cero97-ctrl/LCR-METER/LC-Meter/materiel/DO-35 Diode Horizontal.stp

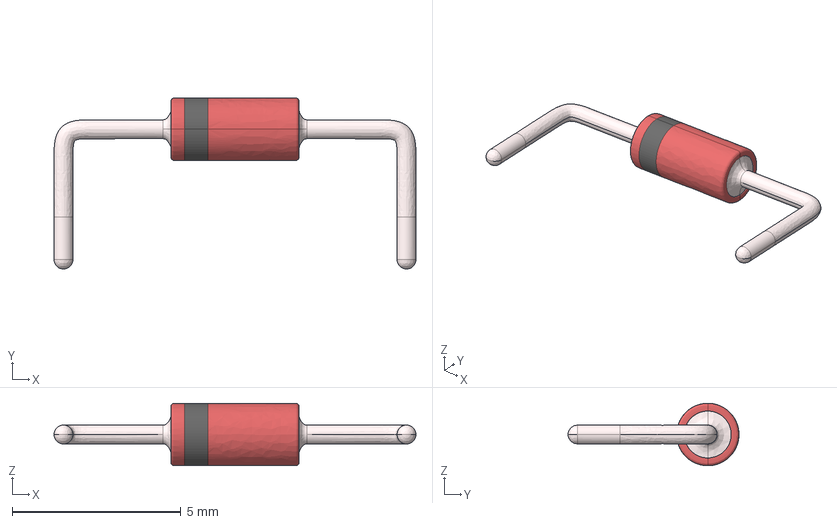
[picture p17: CAD file, 2026-02-04]
LC-Meter/materiel/DO-35 Diode Horizontal.stp
10.7 x 5.07 x 1.85 mm
