cero97-ctrl/LCR-METER/LC-Meter/materiel/2 PIN DG306-5 GREEN - PITCH 5 mm.stp

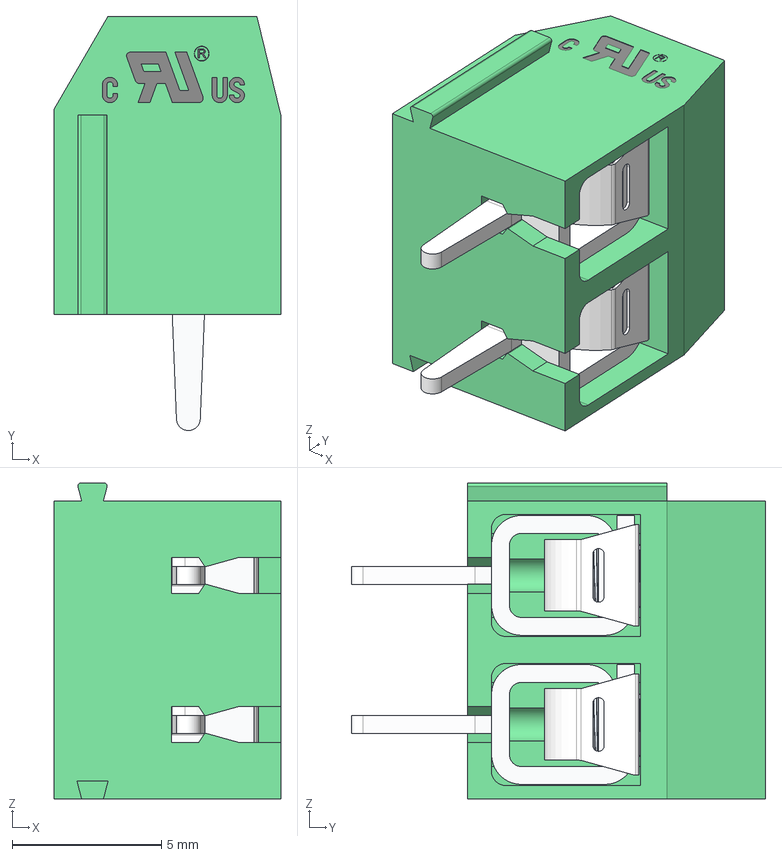
[picture p18: CAD file, 2026-02-04]
LC-Meter/materiel/2 PIN DG306-5 GREEN - PITCH 5 mm.stp
7.60 x 13.9 x 10.6 mm
