cero97-ctrl/LCR-METER/LC-Meter/materiel/Cap Tan TH –Leads L12mm Radial Dipped T350.stp

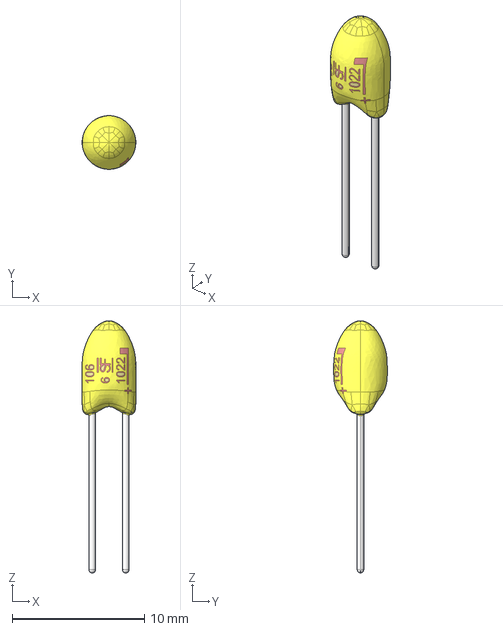
[picture p19: CAD file, 2026-02-04]
LC-Meter/materiel/Cap Tan TH –Leads L12mm Radial Dipped T350.stp
4.06 x 4.06 x 19.0 mm
