cero97-ctrl/LCR-METER/LC-Meter/materiel/Jumper.step

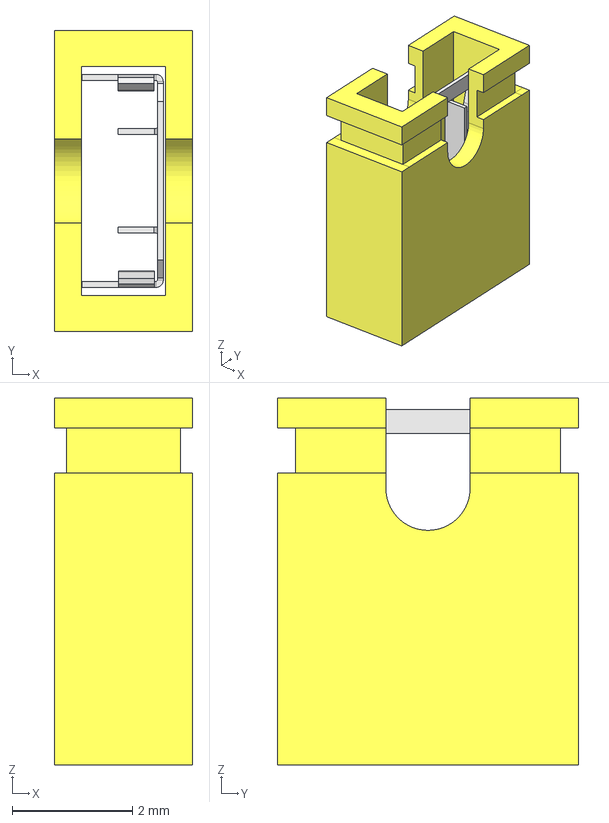
[picture p20: CAD file, 2026-02-04]
LC-Meter/materiel/Jumper.step
2.30 x 5.00 x 6.10 mm
Frame
Jump
