cero97-ctrl/LCR-METER/LC-Meter/materiel/Wirebridge_10.16xD0.6mm.step

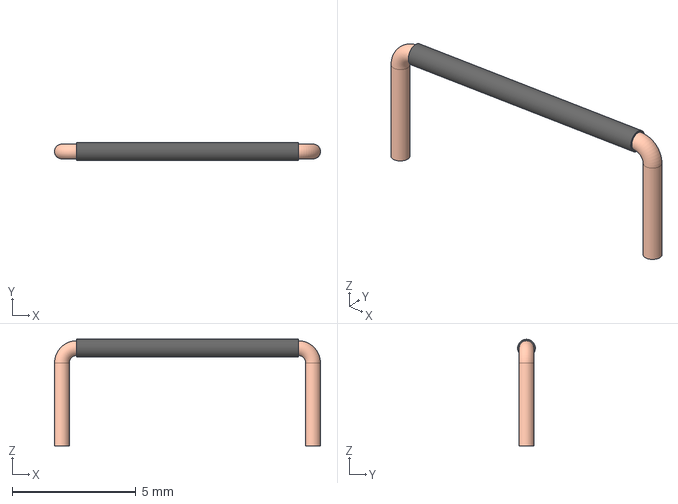
[picture p21: CAD file, 2026-02-04]
LC-Meter/materiel/Wirebridge_10.16xD0.6mm.step
10.8 x 0.719 x 4.31 mm
Wire017
Isolation017
